Reisi/Helena/Documentation/Img/cal_app.png

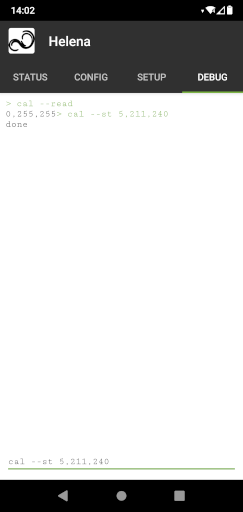
Documentation/Img/cal_app.png
