Reisi/Helena/Documentation/Img/inst_con_02.jpg

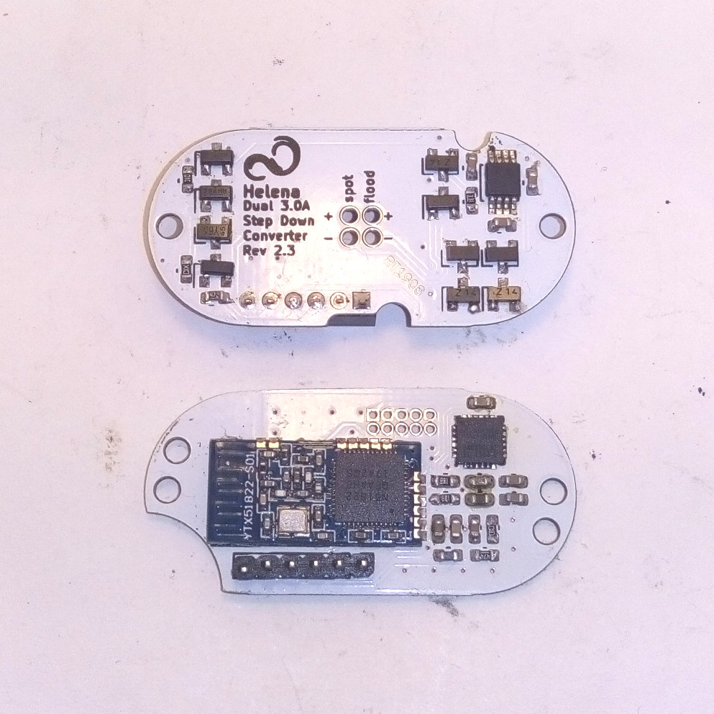
Documentation/Img/inst_con_02.jpg
