Reisi/Helena/Documentation/Img/inst_KD_01.jpg

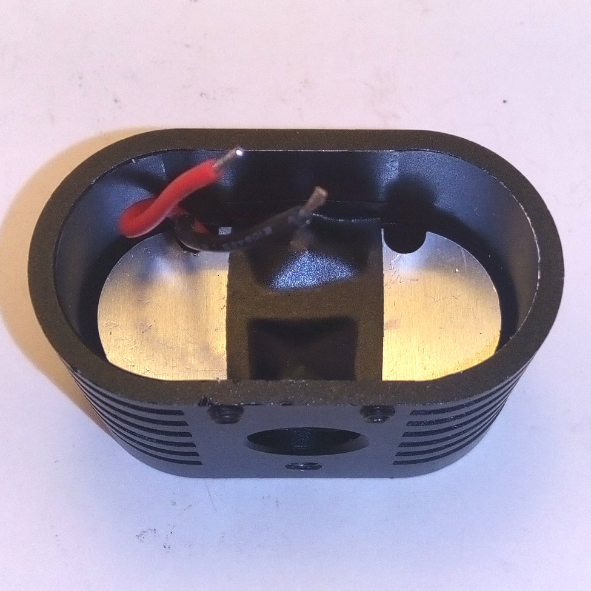
Documentation/Img/inst_KD_01.jpg
