Reisi/Helena/Documentation/Img/inst_KD_02.jpg

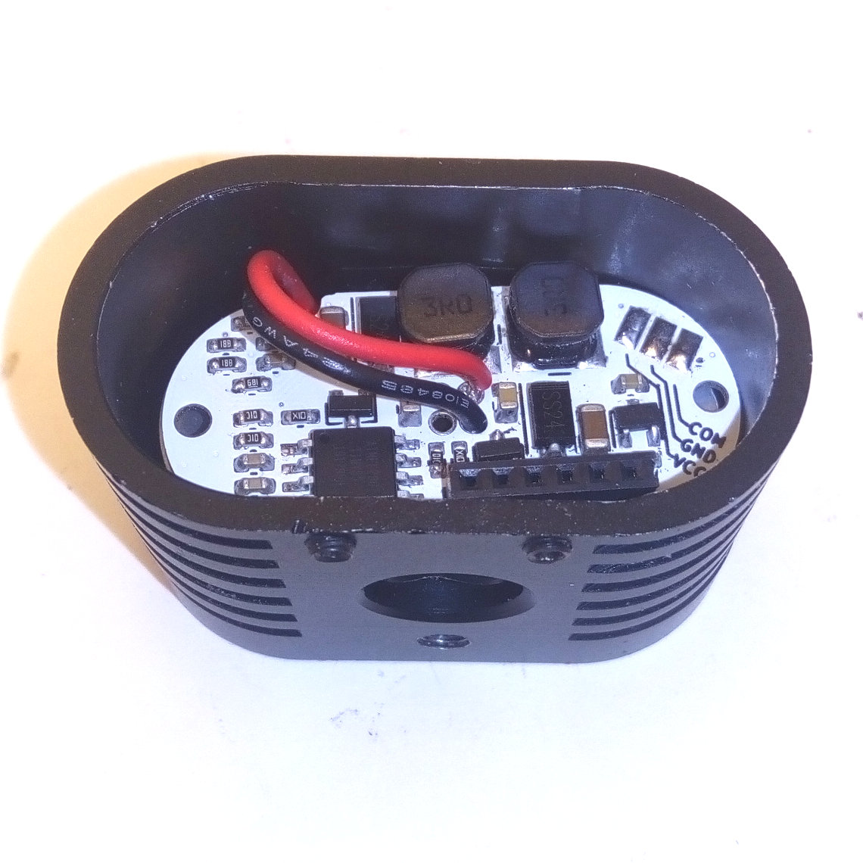
Documentation/Img/inst_KD_02.jpg
