Reisi/Helena/Documentation/Img/inst_KD_03.jpg

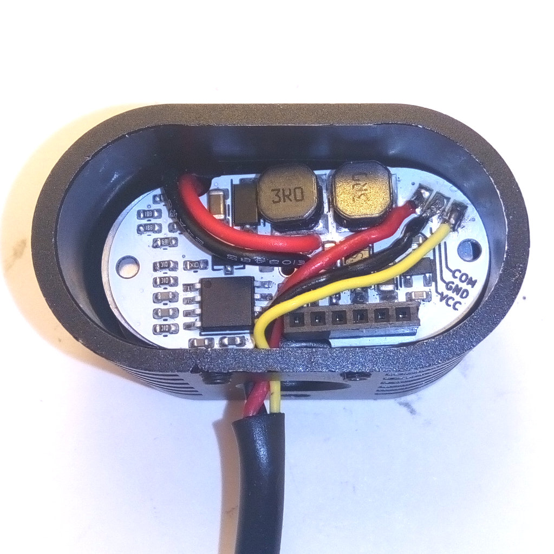
Documentation/Img/inst_KD_03.jpg
