Reisi/Helena/Documentation/Img/inst_KD_04.jpg

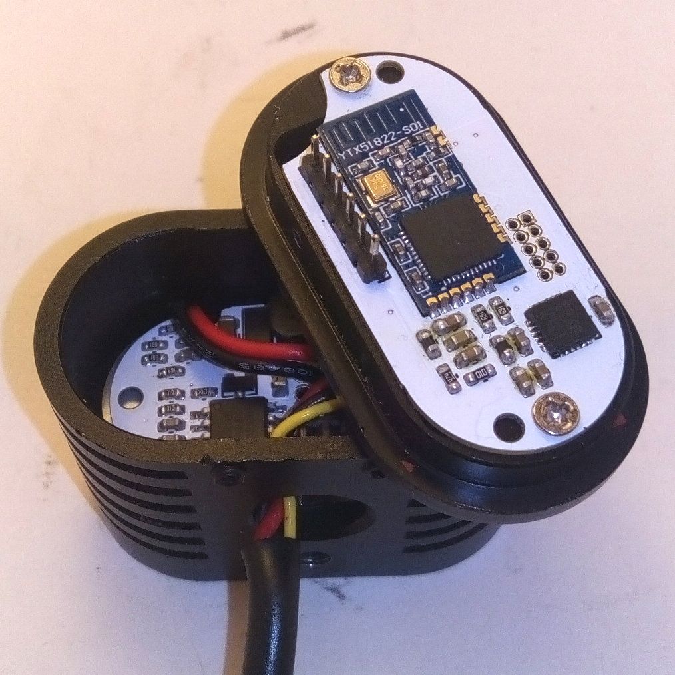
Documentation/Img/inst_KD_04.jpg
