Reisi/Helena/Documentation/Img/inst_KD_05.jpg

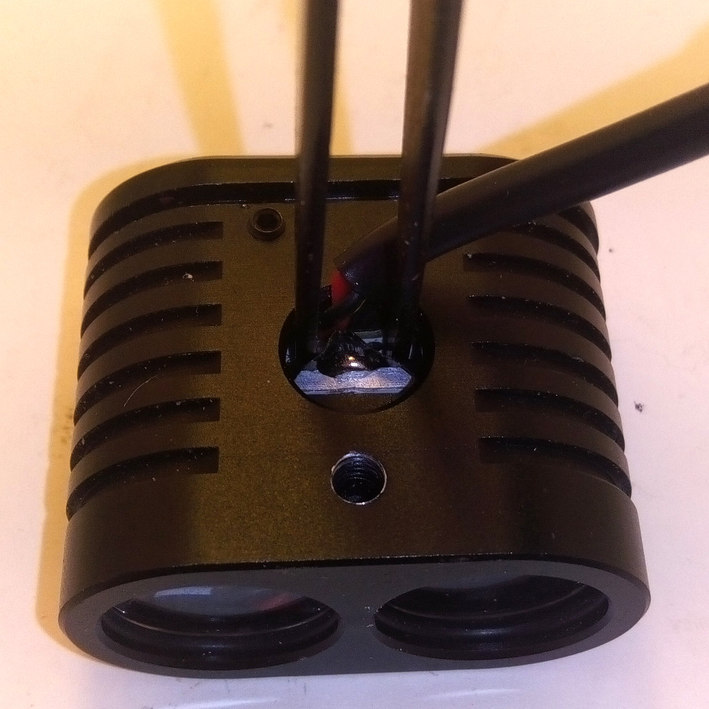
Documentation/Img/inst_KD_05.jpg
