Reisi/Helena/Documentation/Img/inst_YD_02.jpg

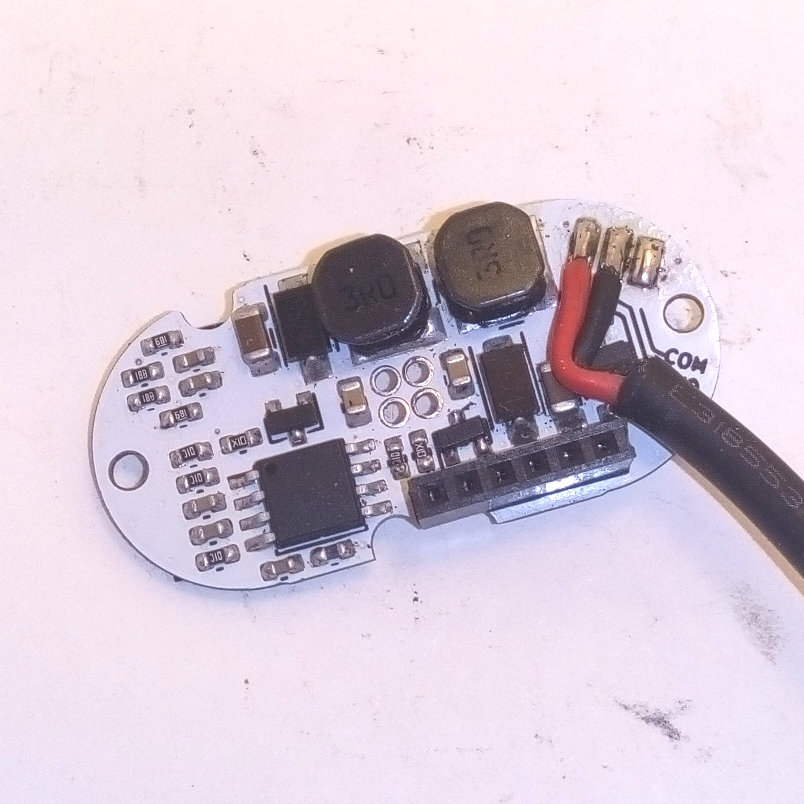
Documentation/Img/inst_YD_02.jpg
