Reisi/Helena/Documentation/Img/inst_YD_04.jpg

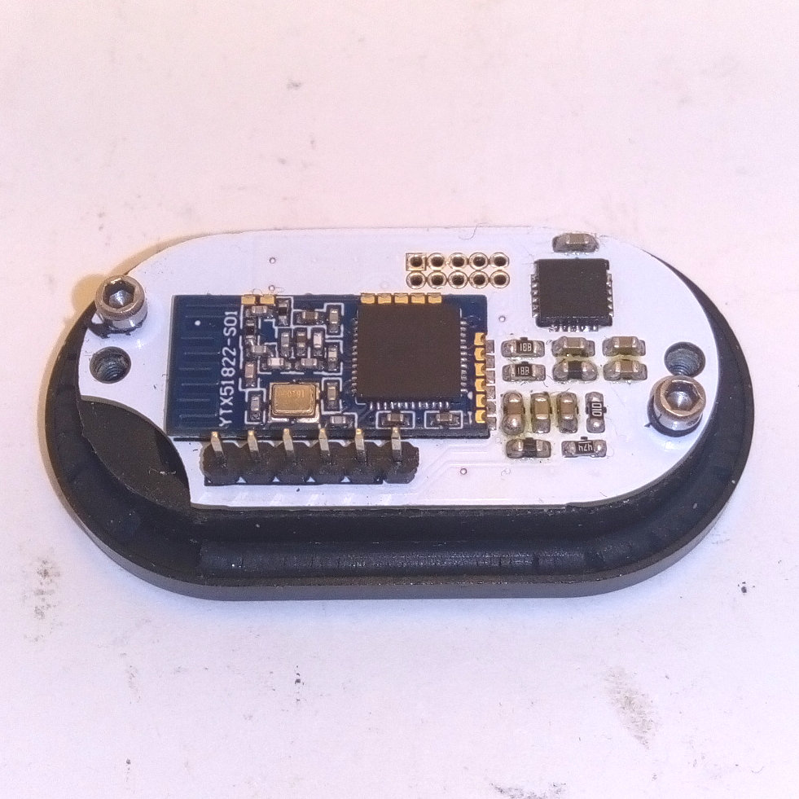
Documentation/Img/inst_YD_04.jpg
