Reisi/Helena/Documentation/Img/inst_YDfull_01.jpg

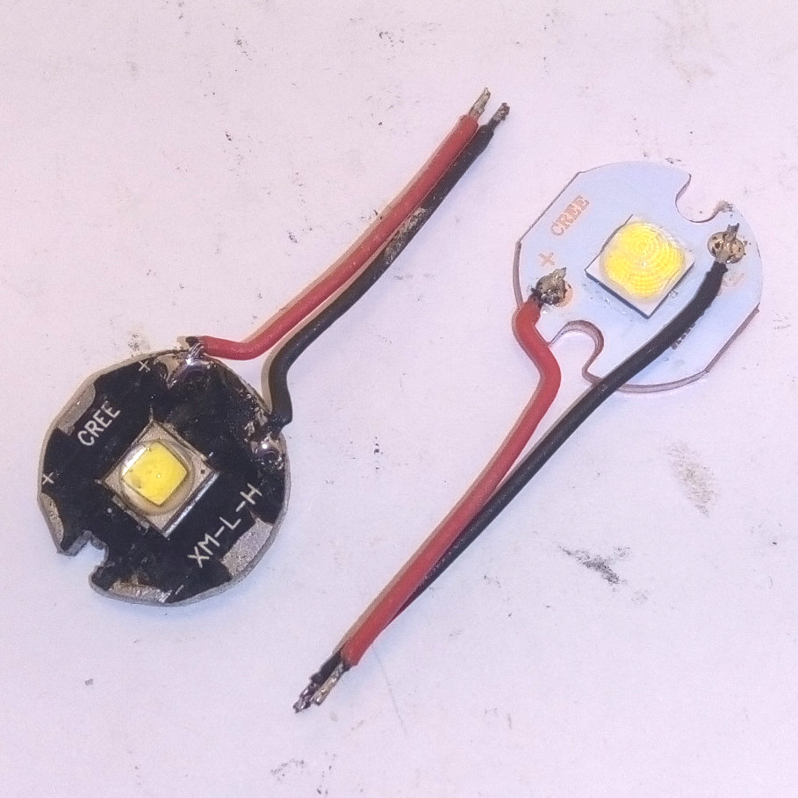
Documentation/Img/inst_YDfull_01.jpg
