Reisi/Helena/Documentation/Img/inst_YDfull_03.jpg

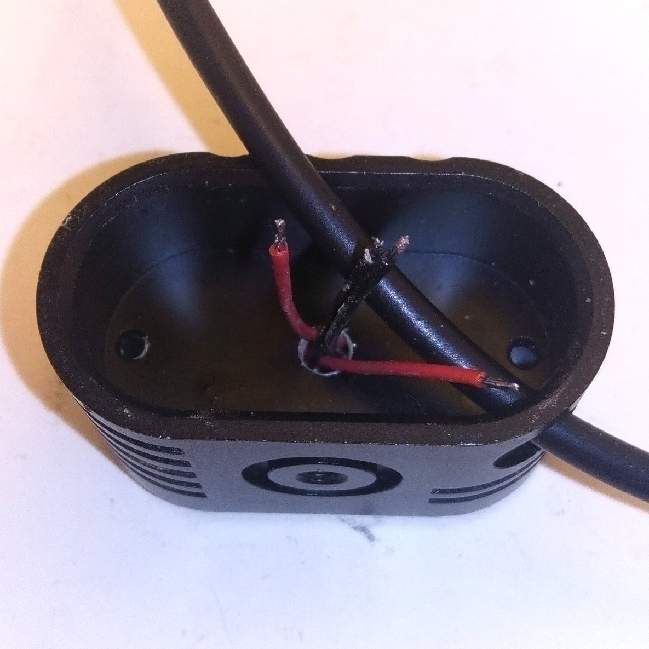
Documentation/Img/inst_YDfull_03.jpg
