Reisi/Helena/Documentation/Img/inst_YDfull_06.jpg

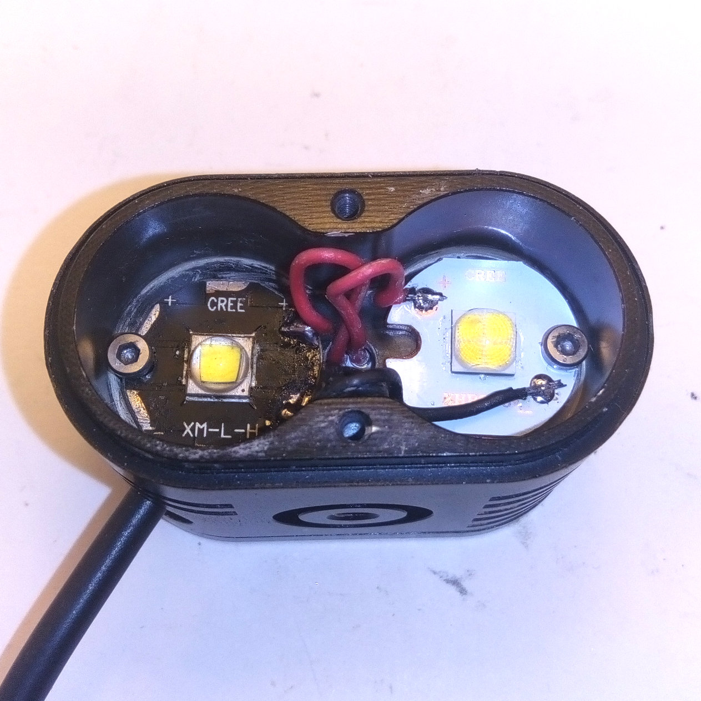
Documentation/Img/inst_YDfull_06.jpg
