Reisi/Helena/Documentation/Img/inst_YDfull_07.jpg

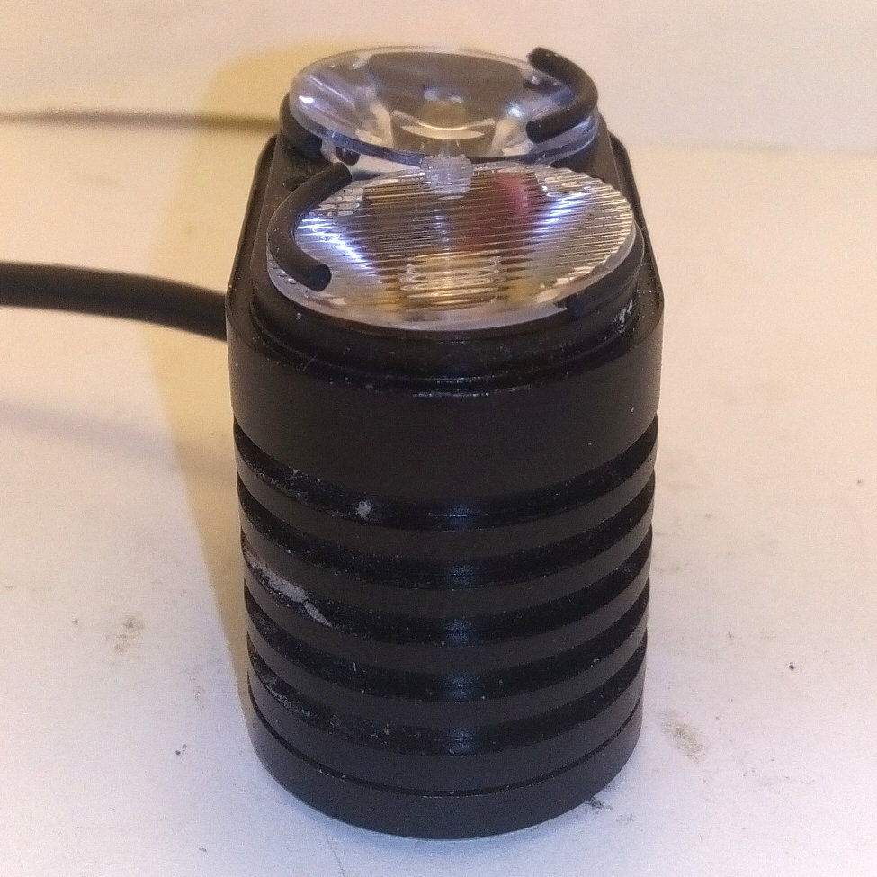
Documentation/Img/inst_YDfull_07.jpg
