Reisi/Helena/Documentation/Img/inst_YDfull_08.jpg

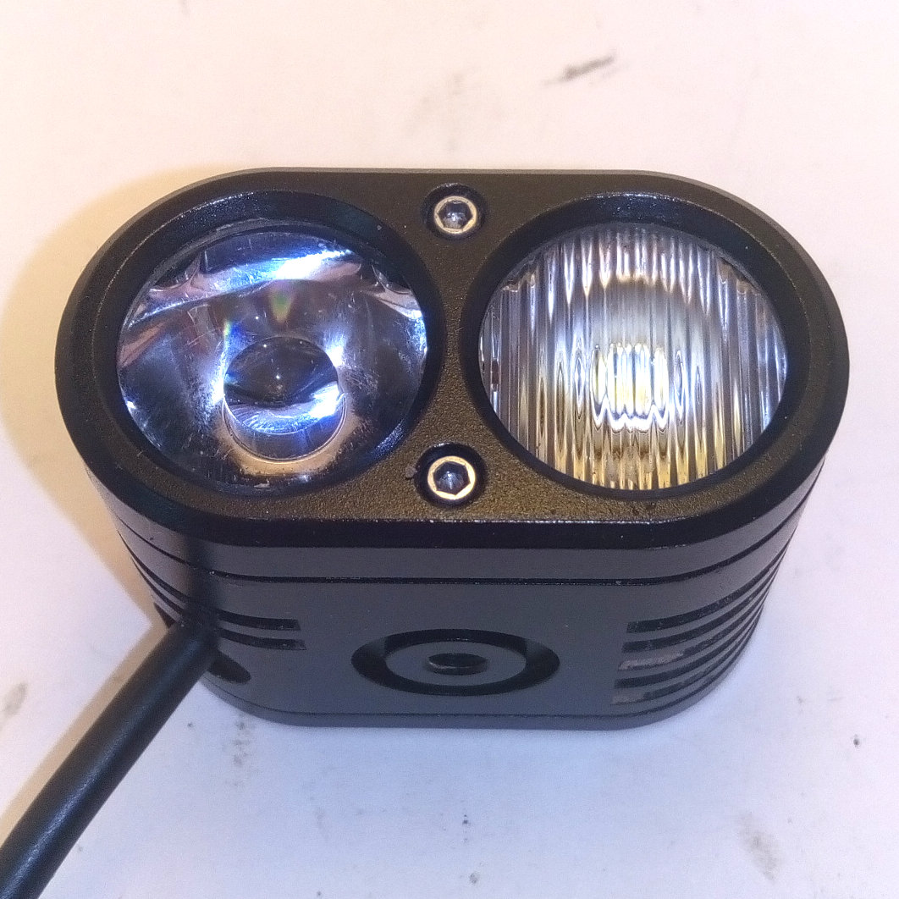
Documentation/Img/inst_YDfull_08.jpg
