Reisi/Helena/Documentation/Img/Xiaomi.jpg

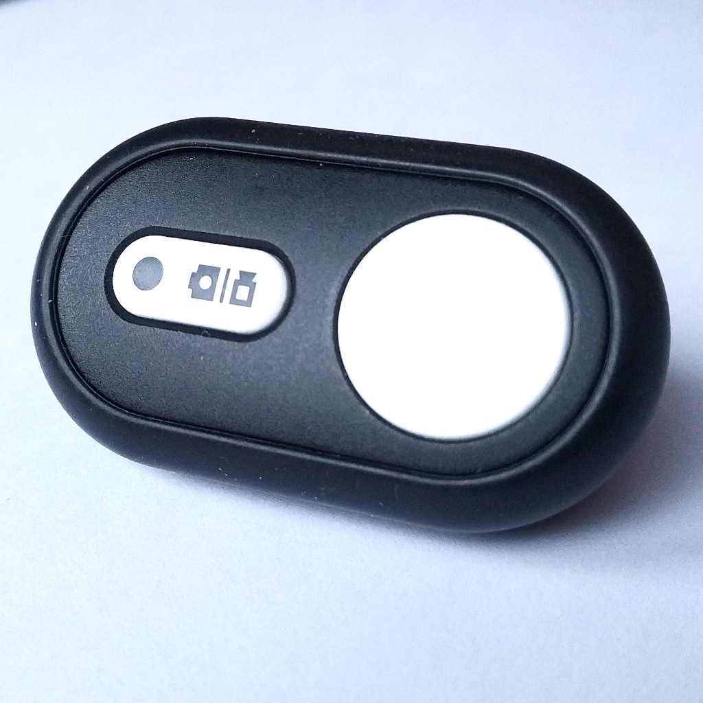
Documentation/Img/Xiaomi.jpg
