Reisi/Helena/Misc/swirl2.png

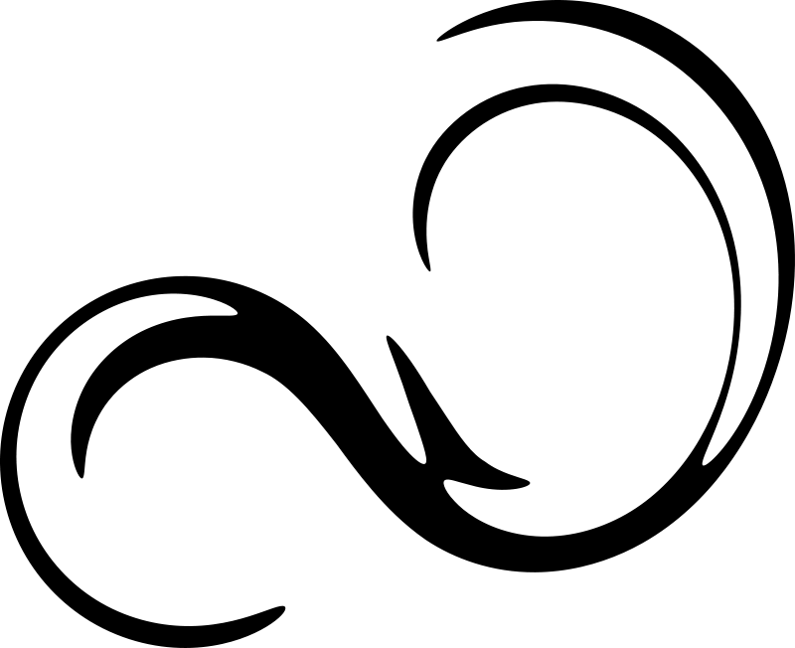
Misc/swirl2.png
