Reisi/Helena/Misc/swirl2_mod.png

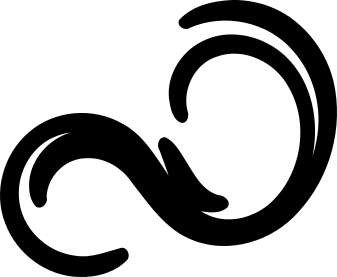
Misc/swirl2_mod.png
