Reisi/Helena/Firmware/Helena_NRF_SDK11/ble/link_management.c

/**
  ******************************************************************************
  * @file    link_management.c
  * @author  Thomas Reisnecker
  ******************************************************************************
  */

/* Includes ------------------------------------------------------------------*/
#include "string.h"
#include "main.h"
#include "ble_advertising.h"
#include "ble_scanning.h"
#include "peer_manager.h"
#include "ble_conn_state.h"
#include "ble_conn_params.h"
#include "link_management.h"
#include "ble_hps.h"
#include "btle.h"
#include "log.h"
#include "fstorage.h"
#include "board_config.h"

/* logger configuration ------------------------------------------------------*/
#define LM_LOG_ENABLED

#ifdef LM_LOG_ENABLED
#include "log.h"
#else
#define LOG_ERROR(...)
#define LOG_INFO(...)
#endif // LM_LOG_ENABLED

/* Private defines -----------------------------------------------------------*/
#define CONN_LOW_POWER          0
#define CONN_LOW_LATENCY        1

/* Private typedef -----------------------------------------------------------*/
typedef struct
{
    lm_advState_t actual;
    lm_advState_t desired;
    btle_advType_t advType;     // the type of advertising
    bool isOpenAdvertising;     // indicating if current advertising should be open to unbonded devices, this will
                                // be reset by advertising timeout or when peripheral device connects,
} advState_t;

typedef struct
{
    lm_scanState_t actual;
    lm_scanState_t desired;
    uint8_t isPeriphControl;    // cumulative counter, if set from several services
} scanState_t;

typedef struct
{
    ble_gap_addr_t  address;    // the address of the device to be connected, this will be reset in the onConnected handler or on connection timeout
    rem_driver_t const* pDriver;// the used driver (if device is a remote, null pointer otherwise)
    uint16_t waitForDisconnect; // the connection handle of the remote, that has to be disconnected first ( if trying to connect to a remote)
    bool isSearchDevice;        // true if the device was found through active scanning, false for whitelist scanning
} deviceConnecting_t;

/* Private macros ------------------------------------------------------------*/
#define ARRAY_SIZE(x)   (sizeof(x)/sizeof(x[0]))

/* Private read only variables and configurations ----------------------------*/
static const ble_adv_modes_config_t advConfig =
{
    .ble_adv_fast_enabled = true,
    .ble_adv_fast_interval = MSEC_TO_UNITS(50, UNIT_0_625_MS),
    .ble_adv_fast_timeout = 30,
    .ble_adv_slow_enabled = true,
    .ble_adv_slow_interval = MSEC_TO_UNITS(1000, UNIT_0_625_MS),
    .ble_adv_slow_timeout = 0,  // no timeout
};

static const ble_scan_modes_config_t scanConfig =
{
    .ble_scan_whitelist_enabled = true,
    .ble_scan_active_scanning   = true,
    .ble_scan_fast_enabled      = true,
    .ble_scan_fast_interval     = MSEC_TO_UNITS(60, UNIT_0_625_MS),
    .ble_scan_fast_window       = MSEC_TO_UNITS(30, UNIT_0_625_MS),
    .ble_scan_fast_timeout      = 30,
    .ble_scan_slow_enabled      = true,
    .ble_scan_slow_interval     = MSEC_TO_UNITS(1280, UNIT_0_625_MS),
    .ble_scan_slow_window       = MSEC_TO_UNITS(11.25, UNIT_0_625_MS),
    .ble_scan_slow_timeout      = 0
};

static const ble_gap_conn_params_t connParamsPeriph[] =
{
    {   // desired connection parameters for low power link
        .min_conn_interval = MSEC_TO_UNITS(500, UNIT_1_25_MS),
        .max_conn_interval = MSEC_TO_UNITS(1000, UNIT_1_25_MS),
        .slave_latency     = 0,
        .conn_sup_timeout  = MSEC_TO_UNITS(4000, UNIT_10_MS)
    },
    {   // desired connection parameters for low latency link
        .min_conn_interval = MSEC_TO_UNITS(100, UNIT_1_25_MS),
        .max_conn_interval = MSEC_TO_UNITS(200, UNIT_1_25_MS),
        .slave_latency     = 0,
        .conn_sup_timeout  = MSEC_TO_UNITS(4000, UNIT_10_MS)
    }
};

static const ble_gap_conn_params_t connParamsCentral =
{
    .min_conn_interval = MSEC_TO_UNITS(10, UNIT_1_25_MS),
    .max_conn_interval = MSEC_TO_UNITS(50, UNIT_1_25_MS),
    .slave_latency     = 0,
    .conn_sup_timeout  = MSEC_TO_UNITS(4000, UNIT_10_MS)
};

static const ble_gap_sec_params_t secParam =
{
    .bond           = 1,                    // perform bonding
    .mitm           = 0,                    // man in the middle protection not required
    .lesc           = 0,                    // LE secure connections not enabled
    .keypress       = 0,                    // keypress notifications not enabled
    .io_caps        = BLE_GAP_IO_CAPS_NONE, // no I/O capabilities
    .oob            = 0,                    // out of bound data not available
    .min_key_size   = 7,
    .max_key_size   = 16,
    .kdist_own.enc  = 1,
    .kdist_own.id   = 1,
    .kdist_peer.enc = 1,
    .kdist_peer.id  = 1,
};

#define FIRST_CONN_PARAMS_UPDATE_DELAY  MAIN_TIMER_TICKS(5000)                       /**< Time from initiating event (connect or start of notification) to first time sd_ble_gap_conn_param_update is called (5 seconds). */
#define NEXT_CONN_PARAMS_UPDATE_DELAY   MAIN_TIMER_TICKS(30000)                      /**< Time between each call to sd_ble_gap_conn_param_update after the first call (30 seconds). */
#define MAX_CONN_PARAMS_UPDATE_COUNT    3

/* Private variables ---------------------------------------------------------*/
static uint8_t uuidType;                    // the uuid type of the light control and helen project service
static advState_t advState;                 // the advertising state
static scanState_t scanState;               // the scanning state
static deviceConnecting_t pendingDevice;    // information of the device, helen is trying to connect to
static uint16_t openPeriphConnHandle;       // the connection handle of the peripheral that connected during open advertising
static uint16_t remoteConnHandle;           // the connection handle of the currently connected remote
static lm_eventHandler_t eventHandler;      // the event handler
static ds_reportHandler_t deleteHandler;    // the deletion report handler, only set if a deletion is pending

/* Private functions ---------------------------------------------------------*/

static void connect(ble_gap_addr_t const* pAddr)
{
    uint32_t errCode;
    ble_gap_scan_params_t const scanParams =
    {
        .interval = scanConfig.ble_scan_fast_interval,
        .window   = scanConfig.ble_scan_fast_window,
        .timeout  = scanConfig.ble_scan_fast_timeout
    };

    // scanning has to be stopped to connect, it will be restarted when connected or on connection timeout
    //nrf_ble_scan_stop();
    ble_scanning_start(BLE_SCAN_MODE_IDLE);
    scanState.actual = LM_SCAN_OFF;



    errCode = sd_ble_gap_connect(pAddr, &scanParams, &connParamsCentral);
    if (errCode == NRF_SUCCESS)
    {
        LOG_INFO("[lm]: Connecting...");
    }
    else
    {
        LOG_ERROR("[lm]: Failed to initiate connection. Error: %d", errCode);
    }
}

static void disconnect(uint16_t connHandle, void * pContext)
{
    UNUSED_PARAMETER(pContext);

    ret_code_t errCode = sd_ble_gap_disconnect(connHandle, BLE_HCI_REMOTE_USER_TERMINATED_CONNECTION);
    if (errCode != NRF_SUCCESS)
    {
        LOG_ERROR("[lm]: disconnect error %d, handle %d", errCode, connHandle);
    }
    else
    {
        LOG_INFO("[lm]: Disconnecting..., handle %d", connHandle);
    }
}

static void sendScanEvent(lm_scanState_t state)
{
    LOG_INFO("[lm]: scan changed, %d (%d)", state, scanState.desired);

    if (eventHandler == NULL)
        return;

    lm_evt_t evt;
    evt.type = LM_EVT_SCAN_MODE_CHANGED;
    evt.evt.newScanState = state;
    eventHandler(&evt);
}

static void sendAdvEvent(lm_advState_t state)
{
    LOG_INFO("[lm]: adv changed, %d (%d)", state, advState.desired);

    if (eventHandler == NULL)
        return;

    lm_evt_t evt;
    evt.type = LM_EVT_ADV_MODE_CHANGED;
    evt.evt.newAdvState = state;
    eventHandler(&evt);
}

/** @brief function to retrieve the next peer manager id depending on the device role
 *
 * @param peerId    the peer id to start from, PM_PEER_ID_INVALID to get the first
 * @param role      BLE_GAP_ROLE_CENTRAL or BLE_GAP_ROLE_PERIPHERAL
 * @return the peer id or PM_PEER_ID_INVALID if no more available
 */
static pm_peer_id_t nextPeerIdGet(pm_peer_id_t peerId, uint8_t role)
{
    pm_peer_data_bonding_t peerData;

    while (1)
    {
        peerId = pm_next_peer_id_get(peerId);
        if (peerId == PM_PEER_ID_INVALID)
            break;

        uint32_t errCode = pm_peer_data_bonding_load(peerId, &peerData);
        if (errCode != NRF_SUCCESS &&
            errCode != NRF_ERROR_NOT_FOUND) // can happen during deletion process
        {
            LOG_ERROR("[lm]: error loading bonding data, %d", errCode);
        }
        else if (peerData.own_role == role)
            break;
    }
    return peerId;
}

/**< returns the number of bonded but unconnected devices depending on the device role */
static uint8_t unconnectedDevices(uint8_t role)
{
    uint8_t cnt = 0;
    pm_peer_id_t peer = nextPeerIdGet(PM_PEER_ID_INVALID, role);

    while (peer != PM_PEER_ID_INVALID)
    {
        uint16_t connHandle;
        APP_ERROR_CHECK(pm_conn_handle_get(peer, &connHandle));
        if (ble_conn_state_status(connHandle) != BLE_CONN_STATUS_CONNECTED)
            cnt++;
        peer = nextPeerIdGet(peer, role);
    }

    return cnt;
}

/** @brief function to set the desired advertising mode
 *
 * @note the actual used advertising mode is reported through the event handler
 *
 * @param[in] mode                  the desired mode
 * @return the return value of ble_advertising_start
 */
static ret_code_t setAdvMode(lm_advState_t mode)
{
    ble_adv_mode_t advMode = BLE_ADV_MODE_IDLE;
    ret_code_t errCode = NRF_SUCCESS;

    /// TODO: is it necessary to check if already in the requested mode? (desired or actual?)

    // convert BTLE_ADV_... modes to BLE_ADV_... modes
    switch (mode)
    {
    case LM_ADV_OFF:
        break;
    case LM_ADV_SLOW:
        advMode = BLE_ADV_MODE_SLOW;
        break;
    case LM_ADV_FAST:
    case LM_ADV_OPEN:
        advMode = BLE_ADV_MODE_FAST;
        break;
    }

    // stop advertising to be able to restart with different settings
    (void)sd_ble_gap_adv_stop();

    advState.isOpenAdvertising = mode == LM_ADV_OPEN ? true : advState.advType == BTLE_ADV_TYPE_ALWAYS_OPEN;

    // check if there are devices to advertise to
    if (!advState.isOpenAdvertising)
    {
        if(unconnectedDevices(BLE_GAP_ROLE_PERIPH) == 0 ||
           ble_conn_state_n_peripherals() == PERIPHERAL_LINK_COUNT)
        {
            // no device to advertise to, advertising is not needed, manually update state and send event
            sendAdvEvent(LM_ADV_OFF);
            advState.actual = LM_ADV_OFF;
            return NRF_SUCCESS;
        }
    }

    if (mode == LM_ADV_OFF)
    {
        // set mode and event manually
        sendAdvEvent(LM_ADV_OFF);
        advState.actual = LM_ADV_OFF;
    }
    else
    {
        errCode = ble_advertising_start(advMode);
        if (errCode == NRF_ERROR_CONN_COUNT)
        {
            // already off, no need for an event
            advState.actual = LM_ADV_OFF;
            return NRF_SUCCESS;
        }
        else
        {
            APP_ERROR_CHECK(errCode);
        }
    }

    return errCode;
}

/**@brief Function for handling advertising events.
 *
 * @details This function will be called for advertising events which are passed to the application.
 *
 * @param[in] ble_adv_evt  Advertising event.
 */
static void advEventHandler(ble_adv_evt_t advEvt)
{
    lm_advState_t newState;

    switch (advEvt)
    {
        // the dedicated LM_ADV_OPEN mode is only used when advertising isn't open all the time
        case BLE_ADV_EVT_FAST:
            if (advState.desired == LM_ADV_SLOW)
            {
                setAdvMode(LM_ADV_SLOW);
                return; // we'll receive a new event with BLE_ADV_EVT_SLOW
            }
            if (advState.advType == BTLE_ADV_TYPE_ALWAYS_OPEN || !advState.isOpenAdvertising)
                newState = LM_ADV_FAST;
            else
                newState = LM_ADV_OPEN;
            break;

        case BLE_ADV_EVT_SLOW:
            newState = LM_ADV_SLOW;
            // open advertising has ended
            if (advState.isOpenAdvertising && advState.advType != BTLE_ADV_TYPE_ALWAYS_OPEN)
            {
                // check if there are devices to advertise to, if not stop advertising
                if (unconnectedDevices(BLE_GAP_ROLE_PERIPH) == 0)
                {
                    (void)sd_ble_gap_adv_stop();
                    newState = LM_ADV_OFF;
                }

                advState.isOpenAdvertising = false;
            }
            break;

        case BLE_ADV_EVT_IDLE:
            newState = LM_ADV_OFF;
            break;

        default:
            return;
    }

    if (newState != advState.actual)
    {
        sendAdvEvent(newState);
        advState.actual = newState;
    }
}

static void advErrorHandler(uint32_t errCode)
{
    LOG_ERROR("[lm]: advertising error %d", errCode);
}

static ret_code_t advertisingInit(lm_init_t const* pInit)
{
    ret_code_t errCode;
    ble_advdata_t advdata = {0}, srdata = {0};
    ble_uuid_t uuids[] =
    {
        {
            .uuid = BLE_UUID_HPS_SERVICE,
            .type = pInit->uuidType
        }
    };

    advState.advType                            = pInit->advType;

    advdata.name_type                      = BLE_ADVDATA_FULL_NAME;
    advdata.flags                          = BLE_GAP_ADV_FLAGS_LE_ONLY_GENERAL_DISC_MODE;
    advdata.uuids_more_available.uuid_cnt  = 1;
    advdata.uuids_more_available.p_uuids   = &uuids[0];
    srdata.include_appearance              = true;

    errCode = ble_advertising_init(&advdata, &srdata, &advConfig, advEventHandler, advErrorHandler);
    APP_ERROR_CHECK(errCode);

    openPeriphConnHandle = BLE_CONN_HANDLE_INVALID;

    return errCode;
}

/** @brief sets the white list
 *  @note  whitelist is only used for scanning, so only devices with central role are added
 *
 * @return bool
 *
 */
static bool setWhitelist()
{
    ret_code_t errCode;

    ble_gap_irk_t* irks[4]; // not scanning for devices with private resolvable address
    ble_gap_addr_t* addrs[4];
    ble_gap_whitelist_t whitelist = {.pp_irks = irks, .pp_addrs = addrs};

    pm_peer_id_t peers[4];
    pm_peer_id_t id = nextPeerIdGet(PM_PEER_ID_INVALID, BLE_GAP_ROLE_CENTRAL);
    uint32_t cnt = 0;

    while (id != PM_PEER_ID_INVALID && cnt < ARRAY_SIZE(peers))
    {
        // no check if already connected necessary, will be done in whiteliste_create()
        uint16_t connHandle = BLE_CONN_HANDLE_INVALID;
        (void)pm_conn_handle_get(id, &connHandle);
        if (ble_conn_state_status(connHandle) != BLE_CONN_STATUS_CONNECTED) // add only unconnected devices
            peers[cnt++] = id;
        id = nextPeerIdGet(id, BLE_GAP_ROLE_CENTRAL);
    }

    //if (cnt == 0)
    //    return false;   /// TODO: whats the reason for returning false in this case?

    errCode = pm_whitelist_create(peers, cnt, &whitelist);
    APP_ERROR_CHECK(errCode);

    errCode = ble_scanning_whitelist_reply(&whitelist);
    APP_ERROR_CHECK(errCode);

    return true;
}

static ret_code_t setScanMode(lm_scanState_t mode)
{
    /// TODO: how to handle searching, if no connections are available?

    ret_code_t errCode = NRF_SUCCESS;
    bool devicesAvailable = (bool)unconnectedDevices(BLE_GAP_ROLE_CENTRAL);
    bool connectionsAvailable = ble_conn_state_n_centrals() < CENTRAL_LINK_COUNT;

    if (connectionsAvailable && (devicesAvailable || mode == LM_SCAN_SEARCH))
    {
        switch (mode)
        {
        case LM_SCAN_OFF:
            errCode = ble_scanning_start(BLE_SCAN_MODE_IDLE);
            break;
        case LM_SCAN_LOW_POWER:
            errCode = ble_scanning_start(BLE_SCAN_MODE_SLOW);
            break;
        case LM_SCAN_LOW_LATENCY:
            errCode = ble_scanning_start(BLE_SCAN_MODE_FAST);
            break;
        case LM_SCAN_SEARCH:
            errCode = ble_scanning_start_without_whitelist(BLE_SCAN_MODE_FAST);
            break;
        }
    }
    // if no connections or devices available event and state need to be set manually
    else
    {
        errCode = ble_scanning_start(BLE_SCAN_MODE_IDLE);
        sendScanEvent(LM_SCAN_OFF);
        scanState.actual = LM_SCAN_OFF;
    }

    if (errCode != NRF_SUCCESS)
    {
        LOG_ERROR("[lm]: scanning start error %d", errCode);
    }

    return errCode;
}

static rem_driver_t const* isRemote(uint8_t const* pData, uint16_t len)
{
    uint8_t i;
    for (i = 0; i < REMOTE_CNT(); i++)
    {
        rem_driver_t const* pDriver = REMOTE_GET(i);
        if (pDriver->is_device(pData, len))
            return pDriver;
    }
    return NULL;
}

static bool isCustomService(uint16_t uuid, uint8_t const* pData, uint16_t len)
{
    ret_code_t errCode;

    ble_uuid_t serviceUuid = {.uuid = uuid, .type = uuidType};
    uint8_t    uuidLen;
    uint8_t    rawUuid[16];

    errCode = sd_ble_uuid_encode(&serviceUuid, &uuidLen, rawUuid);
    if (uuidLen != 16 || errCode != NRF_SUCCESS)
        return false;

    for (uint16_t i = 0; i < len; )
    {
        uint8_t length = pData[i];
        uint8_t type   = pData[i + 1];

        if (type == BLE_GAP_AD_TYPE_128BIT_SERVICE_UUID_MORE_AVAILABLE ||
            type == BLE_GAP_AD_TYPE_128BIT_SERVICE_UUID_COMPLETE)
        {
            for (uint8_t j = 0; j < length/16; j++)
            {
                if (memcmp(rawUuid, &pData[i + 2 + j * 16], sizeof(rawUuid)) == 0)
                    return true;
            }
            return false;
        }

        i += length + 1;
    }

    return false;
}

static void checkAdvReport(ble_gap_evt_adv_report_t const* pAdv)
{
    // additional handling for cases NRF_BLE_SCAN_EVT_FILTER_MATCH and NRF_BLE_SCAN_EVT_WHITELIST_ADV_REPORT
    // safety check, should not happen
    ble_gap_addr_t zero = {0};
    if (memcmp(&pendingDevice.address, &zero, sizeof(ble_gap_addr_t)) != 0)
    {
        LOG_ERROR("[lm]: scanning while device connection is still pending");
    }

    // check if the device is a remote
    rem_driver_t const* pDriver = isRemote(pAdv->data, pAdv->dlen);
    if (pDriver != NULL)
    {
        LOG_INFO("[lm]: remote adv. report received");

        if (!scanState.isPeriphControl) // don't connect if under peripheral control
        {
            pendingDevice.address = pAdv->peer_addr;
            pendingDevice.pDriver = pDriver;
            pendingDevice.isSearchDevice = scanState.actual == LM_SCAN_SEARCH;//pScanEvt->scan_evt_id == NRF_BLE_SCAN_EVT_FILTER_MATCH;
            if (remoteConnHandle == BLE_CONN_HANDLE_INVALID)
                connect(&pAdv->peer_addr); // connect if no remote is connected yet
            else if (scanState.actual == LM_SCAN_SEARCH)
            {                   // disconnect existing remote if a new one was found while searching
                if (pendingDevice.waitForDisconnect != remoteConnHandle) // don't disconnect more than once
                {
                    disconnect(remoteConnHandle, NULL);
                    pendingDevice.waitForDisconnect = remoteConnHandle;
                }
            }
        }
    }
    // check if device is another light
    if (isCustomService(BLE_UUID_HPS_SERVICE, pAdv->data, pAdv->dlen))
    {
        LOG_INFO("[lm]: hps adv. report received");
        pendingDevice.address = pAdv->peer_addr;
        pendingDevice.pDriver = NULL;
        pendingDevice.isSearchDevice = scanState.actual == LM_SCAN_SEARCH;//pScanEvt->scan_evt_id == NRF_BLE_SCAN_EVT_FILTER_MATCH;
        connect(&pAdv->peer_addr);
    }
}

static void scanningEventHandler(ble_scan_evt_t const * const pScanEvt)
{
    lm_scanState_t newState = scanState.actual;

    switch(pScanEvt->ble_scan_event)
    {
    case BLE_SCAN_EVT_IDLE:
    case BLE_SCAN_EVT_PAUSE:
        newState = LM_SCAN_OFF;
        break;

    case BLE_SCAN_EVT_FAST:
        newState = LM_SCAN_SEARCH;
        break;

    case BLE_SCAN_EVT_SLOW:
        // searching for new devices has ended with timeout, restart previous scan mode after searching
        (void)setScanMode(scanState.desired);
        // advertising was stopped while searching, restart with previous or open mode
        (void)setAdvMode(advState.advType == BTLE_ADV_TYPE_AFTER_SEARCH ? LM_ADV_OPEN : advState.desired);
        return; // no event is desired in this case, it will be send after the desired scan mode is set

    case BLE_SCAN_EVT_FAST_WHITELIST:
        newState = LM_SCAN_LOW_LATENCY;
        break;

    case BLE_SCAN_EVT_SLOW_WHITELIST:
        // if low latency scanning is required, restart is required
        if (scanState.desired == LM_SCAN_LOW_LATENCY)
        {
            (void)setScanMode(scanState.desired);
            return; // no event necessary in this case
        }
        newState = LM_SCAN_LOW_POWER; // only set new state if not restarting
        break;

    case BLE_SCAN_EVT_WHITELIST_REQUEST:
        setWhitelist();
        return; // no scan event for this case

    case BLE_SCAN_EVT_ADV_REPORT_RECEIVED:
        checkAdvReport(pScanEvt->p_ble_adv_report);
        return; // no scan event for this case
    }

    if (newState != scanState.actual)
    {
        sendScanEvent(newState);
        scanState.actual = newState;
    }
}

static void scanningErrorHandler(uint32_t errCode)
{
    //APP_ERROR_CHECK(errCode);
    LOG_ERROR("[lm]: scanning error %d", errCode);
}

static ret_code_t scanningInit(uint8_t uuidType)
{
    ret_code_t errCode;

    pendingDevice.waitForDisconnect = BLE_CONN_HANDLE_INVALID;
    remoteConnHandle = BLE_CONN_HANDLE_INVALID;

    errCode = ble_scanning_init(&scanConfig, scanningEventHandler, scanningErrorHandler);
    APP_ERROR_CHECK(errCode);

    return errCode;
}

/**@brief Function for handling a Connection Parameters error.
 *
 * @param[in] nrf_error  Error code containing information about what went wrong.
 */
static void connParamsErrorHandler(uint32_t errCode)
{
    //APP_ERROR_CHECK(errCode);
    LOG_ERROR("[lm]: connection params error %d", errCode);
}

/**@brief Function for initializing the Connection Parameters module.
 */
static ret_code_t connParamsInit(void)
{
    ret_code_t             errCode;
    ble_conn_params_init_t cpInit = {0};

    cpInit.p_conn_params                  = (ble_gap_conn_params_t*)&connParamsPeriph[CONN_LOW_POWER];
    cpInit.first_conn_params_update_delay = FIRST_CONN_PARAMS_UPDATE_DELAY;
    cpInit.next_conn_params_update_delay  = NEXT_CONN_PARAMS_UPDATE_DELAY;
    cpInit.max_conn_params_update_count   = MAX_CONN_PARAMS_UPDATE_COUNT;
    cpInit.start_on_notify_cccd_handle    = BLE_GATT_HANDLE_INVALID;
    cpInit.disconnect_on_fail             = true;
    cpInit.evt_handler                    = NULL;
    cpInit.error_handler                  = connParamsErrorHandler;

    errCode = ble_conn_params_init(&cpInit);
    if (errCode != NRF_SUCCESS)
        LOG_ERROR("[lm]: conn param init error %d", errCode);

    return errCode;
}
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
